PaladinBIGDan2077/Blinkenbits-formerly-Memory-Teaching-Tool/KiCad/Practice/Memory-Teaching-Tool/Memory-Teaching-Tool.kicad_pcb

## KiCad design esp32-smart-speaker-schema/esp32-smart-speaker-schema.kicad_sch

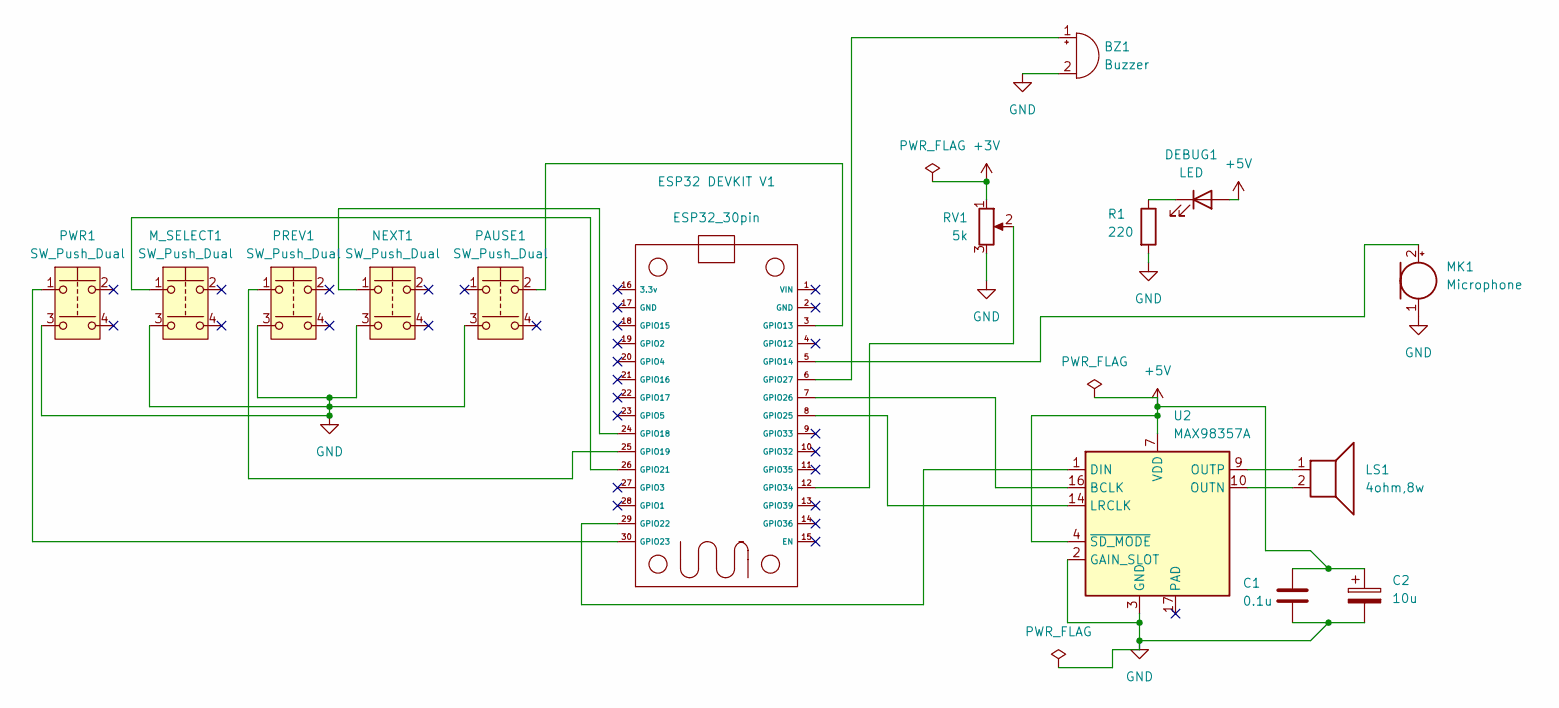
[picture p2: schematic esp32-smart-speaker-schema.kicad_sch]

Parts:
BZ1: Buzzer
C1: 0.1u
C2: 10u
DEBUG1: LED
ESP32 DEVKIT V1: ESP32_30pin
LS1: 4ohm,8w
MK1: Microphone
M_SELECT1: SW_Push_Dual
NEXT1: SW_Push_Dual
PAUSE1: SW_Push_Dual
PREV1: SW_Push_Dual
PWR1: SW_Push_Dual
R1: 220
RV1: 5k
U2: MAX98357A; TQFN-16-1EP_3x3mm_P0.5mm_EP1.23x1.23mm

Connections:
+3V: RV1.1
+5V: C1.1, C2.1, DEBUG1.2 (A), U2.4 (~SD_MODE), U2.7 (VDD), U2.8 (VDD)
GND: BZ1.2 (-), C1.2, C2.2, MK1.1 (-), M_SELECT1.3, NEXT1.3, PAUSE1.3, PREV1.3, PWR1.3, R1.2, RV1.3, U2.2 (GAIN_SLOT), U2.3 (GND), U2.11 (GND), U2.15 (GND)
unnamed: BZ1.1 (+), ESP32 DEVKIT V1.6 (GPIO27)
unnamed: DEBUG1.1 (K), R1.1
unnamed: ESP32 DEVKIT V1.3 (GPIO13), PAUSE1.2
unnamed: ESP32 DEVKIT V1.5 (GPIO14), MK1.2 (+)
unnamed: ESP32 DEVKIT V1.7 (GPIO26), U2.16 (BCLK)
unnamed: ESP32 DEVKIT V1.8 (GPIO25), U2.14 (LRCLK)
unnamed: ESP32 DEVKIT V1.12 (GPIO34), RV1.2
unnamed: ESP32 DEVKIT V1.24 (GPIO18), NEXT1.1
unnamed: ESP32 DEVKIT V1.25 (GPIO19), PREV1.1
unnamed: ESP32 DEVKIT V1.26 (GPIO21), M_SELECT1.1
unnamed: ESP32 DEVKIT V1.29 (GPIO22), U2.1 (DIN)
unnamed: ESP32 DEVKIT V1.30 (GPIO23), PWR1.1
unnamed: LS1.1, U2.9 (OUTP)
unnamed: LS1.2, U2.10 (OUTN)
