PaladinBIGDan2077/Blinkenbits-formerly-Memory-Teaching-Tool/WordOutputter/FanController/I2C_READ_DATA.v

module I2C_READ_DATA(
   output reg NO_ACK ,
   input  				RESET_N ,
	input       		PT_CK,
	input       [7:0] BYTE_NUM , 
	input       [7:0]	SLAVE_ADDRESS , 
	input       		GO,
	input       		SDAI,
	output reg  		SDAO,
	output reg  		SCLO,
	output reg  		 END_OK , 
	output reg  [15:0] DATA , 
	//for TEST
	output reg  [5:0] ST ,
	output reg  [3:0] CNT,
	output reg  [8:0] A ,
	output reg  [3:0] BYTE
);
//=======================================================
//  REG/WIRE declarations
//=======================================================
reg    [7:0]DELY ;   

  
//=======================================================
//  Parameter declarations
//=======================================================

always @( negedge RESET_N or posedge  PT_CK )begin
if (!RESET_N  ) begin 
            NO_ACK <=0;
            ST <=0;
		      SDAO   <=1; 
	         SCLO   <=1;
	         CNT    <=0;
	         END_OK <=1;
	         BYTE   <=0;
				DATA <=0;  
end 				
else 
	  case (ST)
	    0: begin  
		      SDAO   <=1; 
	         SCLO   <=1;
	         CNT    <=0;
	         END_OK <=1;
	         BYTE   <=0;
				DATA <=0;
	         if (GO) ST  <=30 ;							
		    end		  
	  //----I2C READ-COMMAND---
	    1: begin  //start 
		      ST <=2 ; 
			   { SDAO,  SCLO } <= 2'b01; 
				A <= {SLAVE_ADDRESS | 1  ,1'b1 };//READ COMMAND
		    end
	    2: begin  //start 
		      ST <=3 ; 
			   { SDAO,  SCLO } <= 2'b00; 
		    end
			 
	    3: begin  //start 
		      ST <=4 ; 
			   { SDAO, A } <= { A ,1'b0 }; 
		    end
	    4: begin
		      ST <=5 ; 
			   SCLO <= 1'b1 ; 
				CNT <= CNT +1 ;
		    end
			 
	    5: begin  
			   SCLO <= 1'b0 ; 
			   if (CNT ==9) begin
				    ST <= 6 ; 
					 NO_ACK <= SDAI ;
				 end
				 else ST <= 2;
		    end			 
     //-----DATA READ---
	    6: begin 
		      ST <=7 ; 
			   {SDAO , SCLO} <= 2'b10; 
				CNT <=0 ;
		    end
	    7: begin  
		      ST <=8 ;  
				DELY <=0;
			   SCLO <= 1'b1 ; 
				if (CNT!=8) DATA[15:0]  <= { DATA[14:0], SDAI };
				CNT <= CNT +1 ;
		    end			 
	    8: begin  		 
		    DELY <=DELY+1 ;
			 SCLO <= 1'b0 ; 
			 if (DELY ==2)  begin 			    
			    if (CNT ==8) begin
				      ST <= 7;
					   if (BYTE  == BYTE_NUM  )  SDAO <= 1'b1 ; 
					   else  
					   SDAO <= 1'b0 ;
				 end
			    else if (CNT == 9)  
				    begin 
					   BYTE <= BYTE +1 ;   ST <= 9; 
					 end
				 else ST <= 7;
			 end	 
		    end
	    9: begin
		     if  ( BYTE >  BYTE_NUM  ) ST <=10 ; 
			   else ST <=6 ; 
			   
         end
	    10: begin          //stop
		      ST <=11 ; 
			   { SDAO,  SCLO } <= 2'b00; 
         end
	    11: begin          //stop
		      ST <=12 ; 
			   { SDAO,  SCLO } <= 2'b01; 
         end
	    12: begin          //stop
		      ST <=13 ; 
			   { SDAO,  SCLO } <= 2'b11; 
         end	
		 13:	 
			  begin
		      ST     <= 30; 
				END_OK <= 1;
		      SDAO   <=1; 
	         SCLO   <=1;
	         CNT    <=0;
	         BYTE <=0;				
		     end
		//--- END ---
		30: begin
            if (!GO) ST  <=31;
          end
 		31: begin 
		    ST  <=1; END_OK<=0;
          end		 			  	  
	  endcase 
  end

endmodule
